PoliTeK/PoliKick/images/Front_PAnel.png

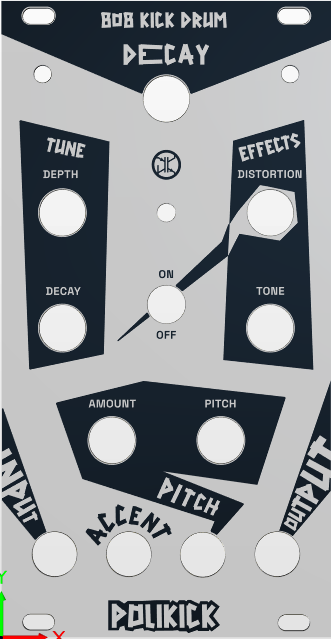
images/Front_PAnel.png
