PoliTeK/PoliKick/Simulations/PoliKick.asc

AccentCV: voltage; 0V
C1: cap; 10n
C2: cap; 220n
C3: cap; 5.6n
C4: cap; 15n
C5: cap; 15n
C6: cap; 68n
C7: cap; {C}
D1: diode
D2: diode
D3: diode
D4: diode; Dx
D5: diode; Dx
DecayLog: res; 42k
DistortionGainLog: res; 100k
E1: e; 0.2
Pitch: res; 4.7k
PitchCV: voltage; 0V
Q1: pnp
Q2: npn
Q3: pnp
Q4: npn
Q5: npn
R1: res; 39k
R2: res; 33k
R3: res; 100k
R4: res; 100k
R5: res; 22k
R6: res; 120k
R7: res; 100k
R8: res; 10k
R9: res; 1Meg
R10: res; 50k
R11: res; 50k
R12: res; 2k
R13: res; 100k
R14: res; 100k
R15: res; 14k
R16: res; 1Meg
R17: res; 100k
R18: res; 47k
R19: res; 470k
R20: res; 10
R21: res; 18k
R22: res; 10
R23: res; 10
R24: res; 10
Tone: res; 50k
TuneDecay: res; 100k
TuneDepth: res; 10k
U1: TL072
U2: TL072
U3: TL072
U4: TL072
V1: voltage; 0
Vcc: battery; 12V
Vee: battery; 12V
Vi: voltage; PULSE(0 10 1ms 200u 200u 200ms 1s)
Vp1: voltage; PULSE(0 5 1 200u 200u 200ms 10s)
Vp2: voltage; PULSE(0 3 2ms 200u 200u 200ms 10s)
Vp3: voltage; PULSE(0 7 3s 200u 200u 200ms 10s)
Vp: voltage; PULSE(0 10 1ms 200u 200u 200ms 10s)
X1: SPDT
Named nets: 0, Vcc, Vee, Vi, AccentCV, PitchCV, Vout, WavOut, Vp
Gate to trigger
.tran 0 5s 0 100u
.step param PitchCV 0 5 1
.step param AccentCV 0V 5V 1V
.step param TuneDecay 10 100k 10k
.step param TuneDepth 10 10k 1k
.step param Pitch 10 100k 10k
.step param DecayLog 10 50k 5k
.step param Tone 10 50k 5k
.step param Distorsion 10 100k 10k
Pot 100k
> 5V: ON
.model Dx D(Vfwd=1.4)
.lib TL07xTI.txt
.wave softclip.wav 16 44.1k V(WavOut)
Scale Vout and save to .wav file
.step param C 1u 10u 1u
