PoliTeK/PoliKick/Simulations/SPDT.asc

A1: inv; td=10n Vhigh=5
S1: sw; MSW
S2: sw; MSW
Named nets: 1, 2, 3, +, -
.model MSW SW(Ron=25u Roff=1G Vt=0.1 Vh=0.1)
